Joel-Eagles/Recessed-Unifi-Entry-Senser/Assets/PXL_20260328_174757136.jpg

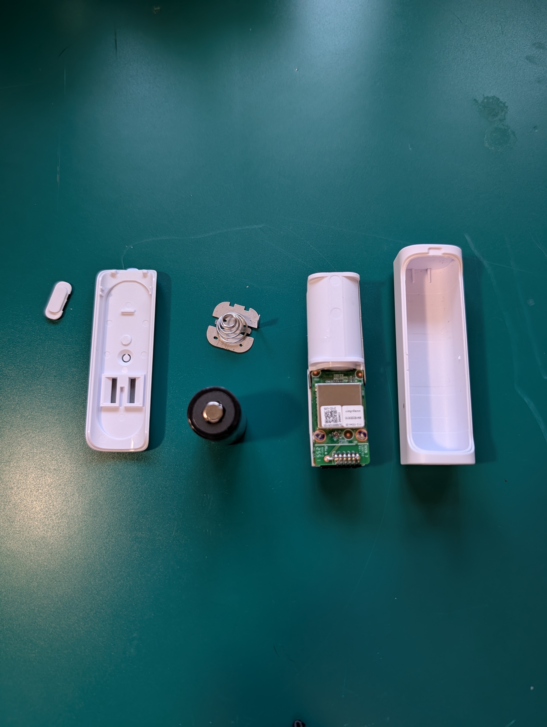
Assets/PXL_20260328_174757136.jpg
