Joel-Eagles/Recessed-Unifi-Entry-Senser/Assets/PXL_20260328_175808920.jpg

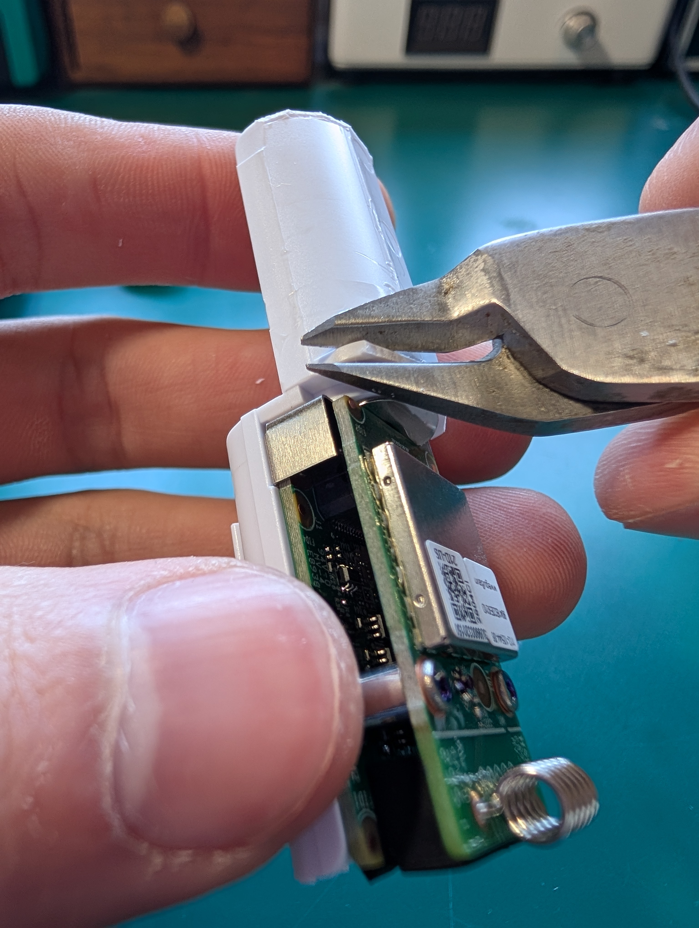
Assets/PXL_20260328_175808920.jpg
