Joel-Eagles/Recessed-Unifi-Entry-Senser/Assets/PXL_20260328_175924456.jpg

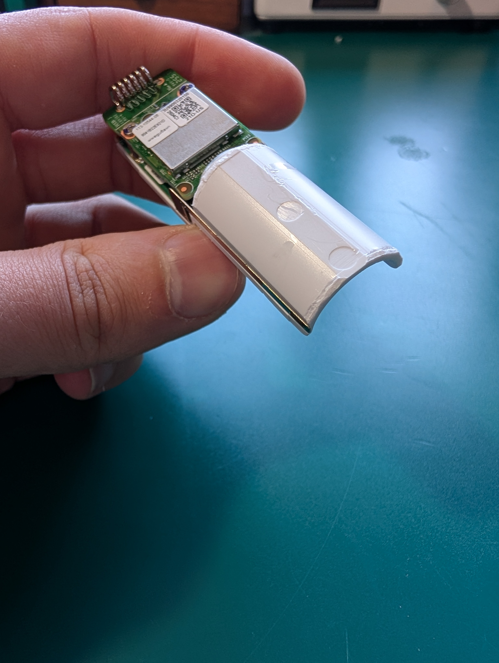
Assets/PXL_20260328_175924456.jpg
