Joel-Eagles/Recessed-Unifi-Entry-Senser/Assets/PXL_20260329_185001049.jpg

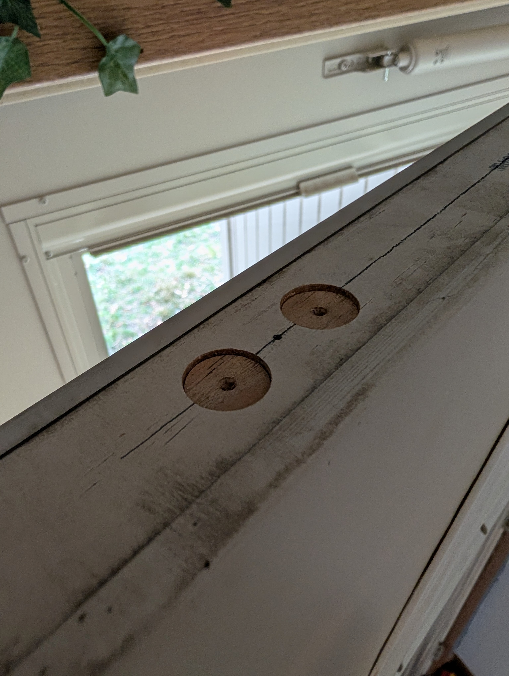
Assets/PXL_20260329_185001049.jpg
