Joel-Eagles/Recessed-Unifi-Entry-Senser/Assets/PXL_20260329_191639085.jpg

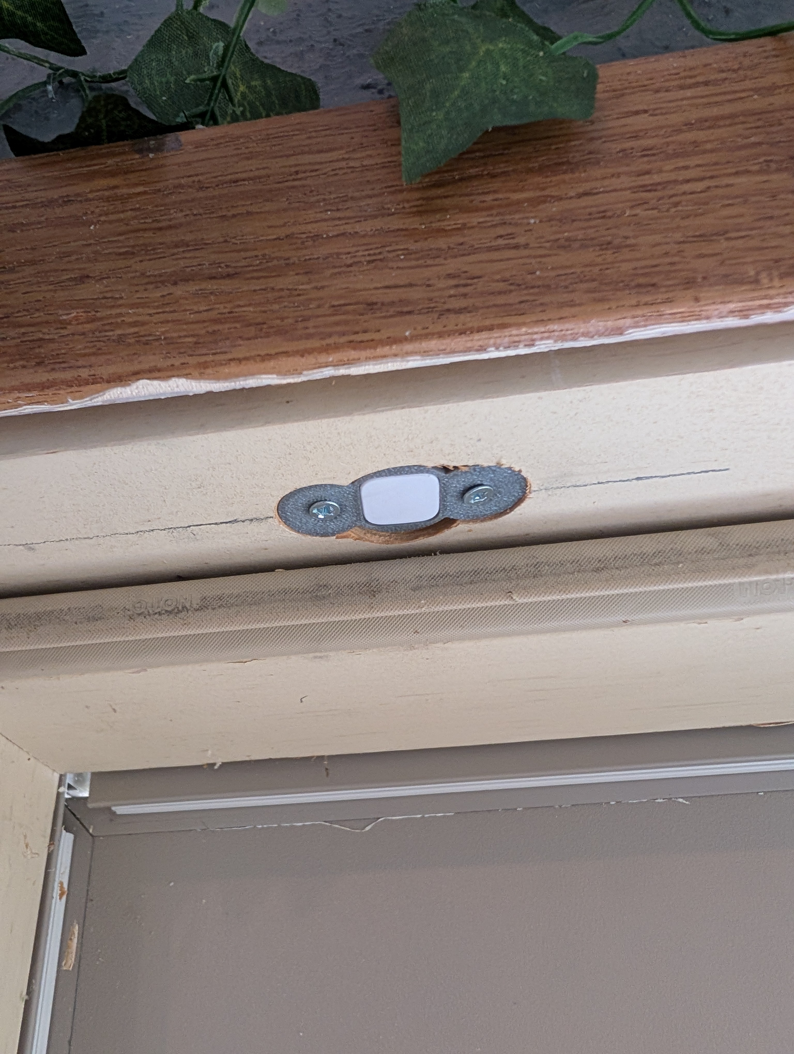
Assets/PXL_20260329_191639085.jpg
