Joel-Eagles/Recessed-Unifi-Entry-Senser/Assets/PXL_20260329_191658487.jpg

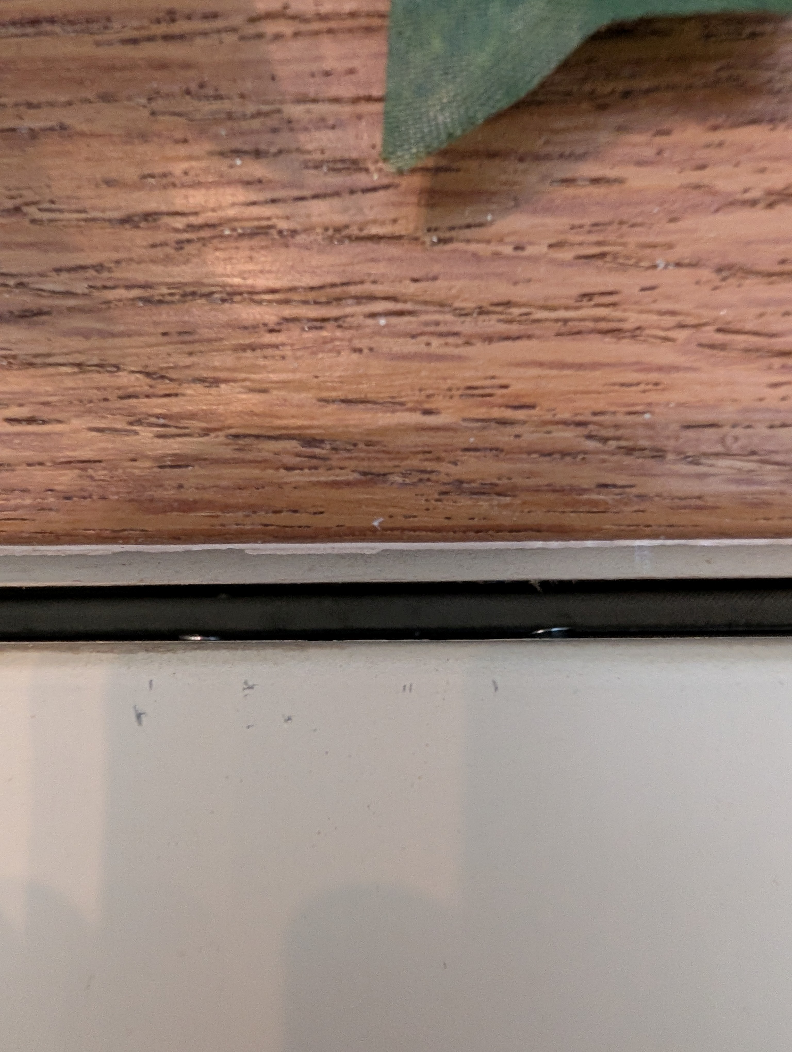
Assets/PXL_20260329_191658487.jpg
